dumblob/lingo_splix_board/design/evolution/v0.0.1_kbd-original_DE-s.jpg

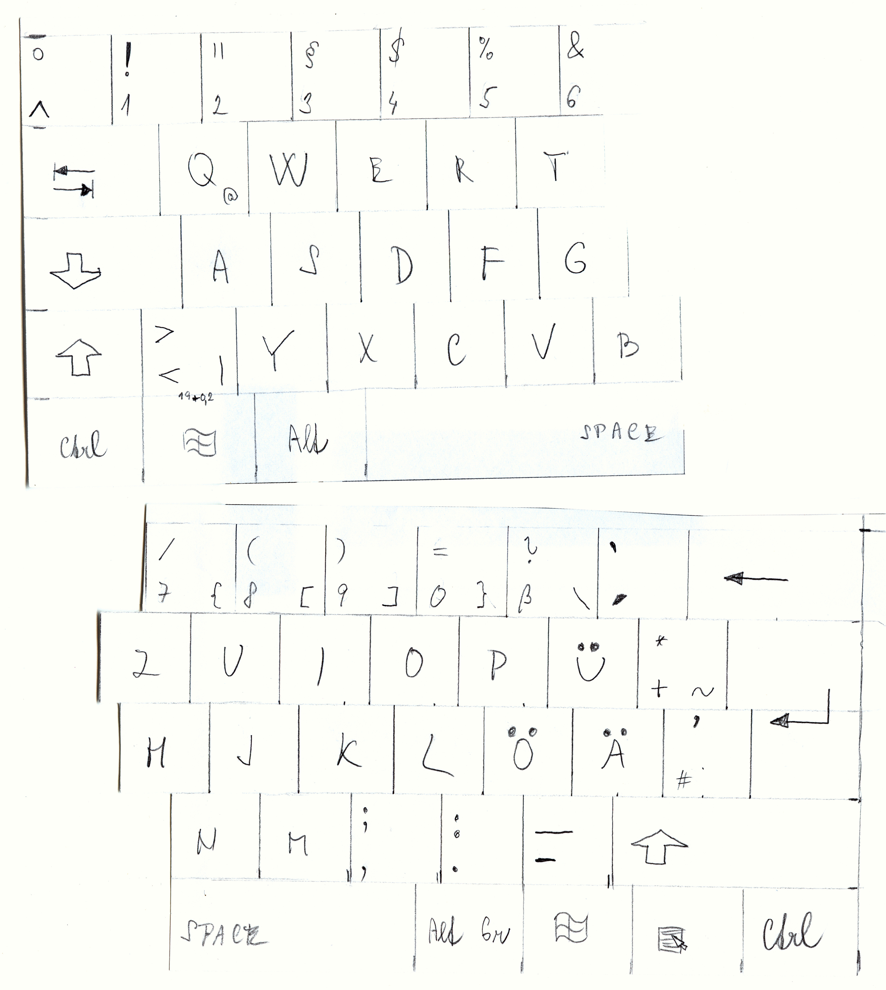
design/evolution/v0.0.1_kbd-original_DE-s.jpg
