dumblob/lingo_splix_board/design/evolution/v0.2_kbd-s.jpg

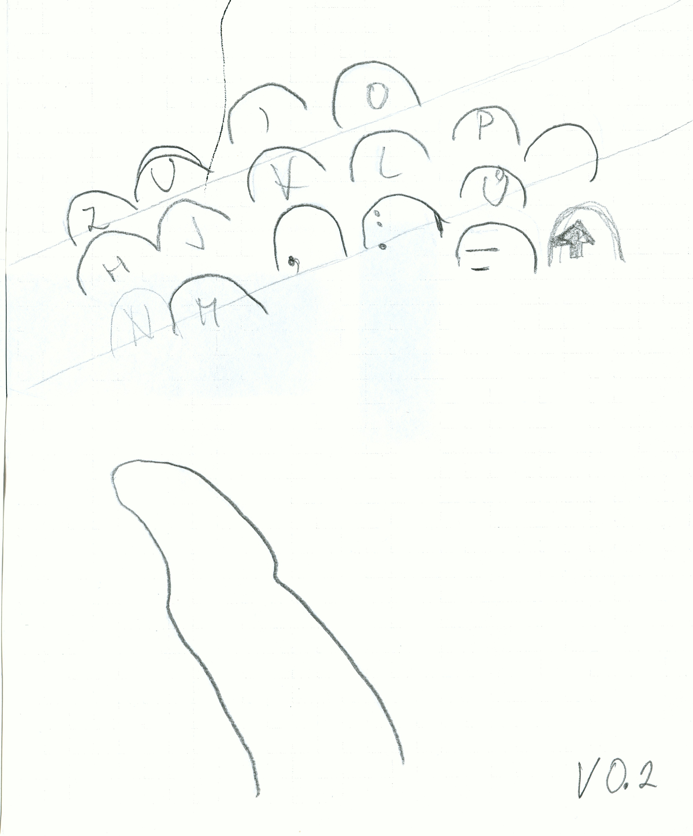
design/evolution/v0.2_kbd-s.jpg
