dumblob/lingo_splix_board/design/evolution/v0.3_kbd-s.jpg

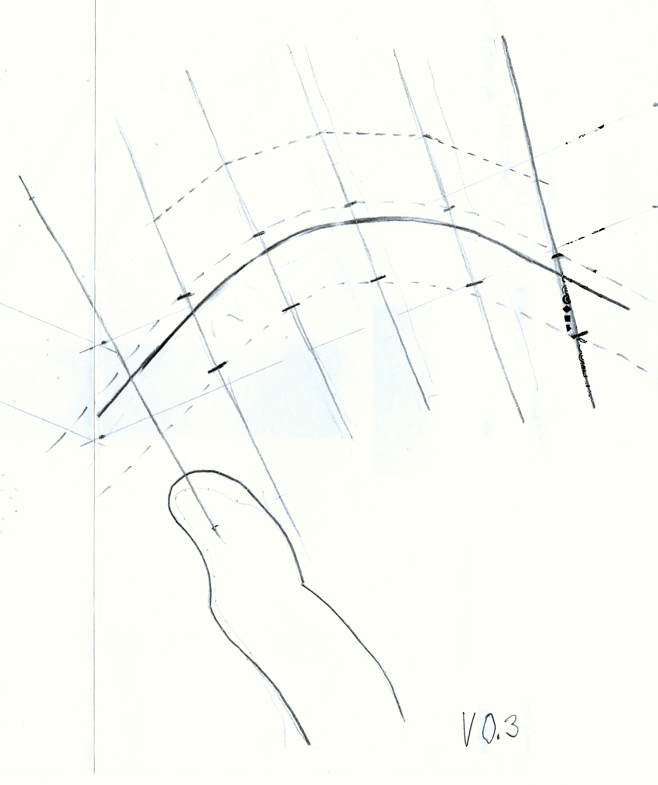
design/evolution/v0.3_kbd-s.jpg
