dumblob/lingo_splix_board/design/evolution/v0.4_kbd-s.jpg

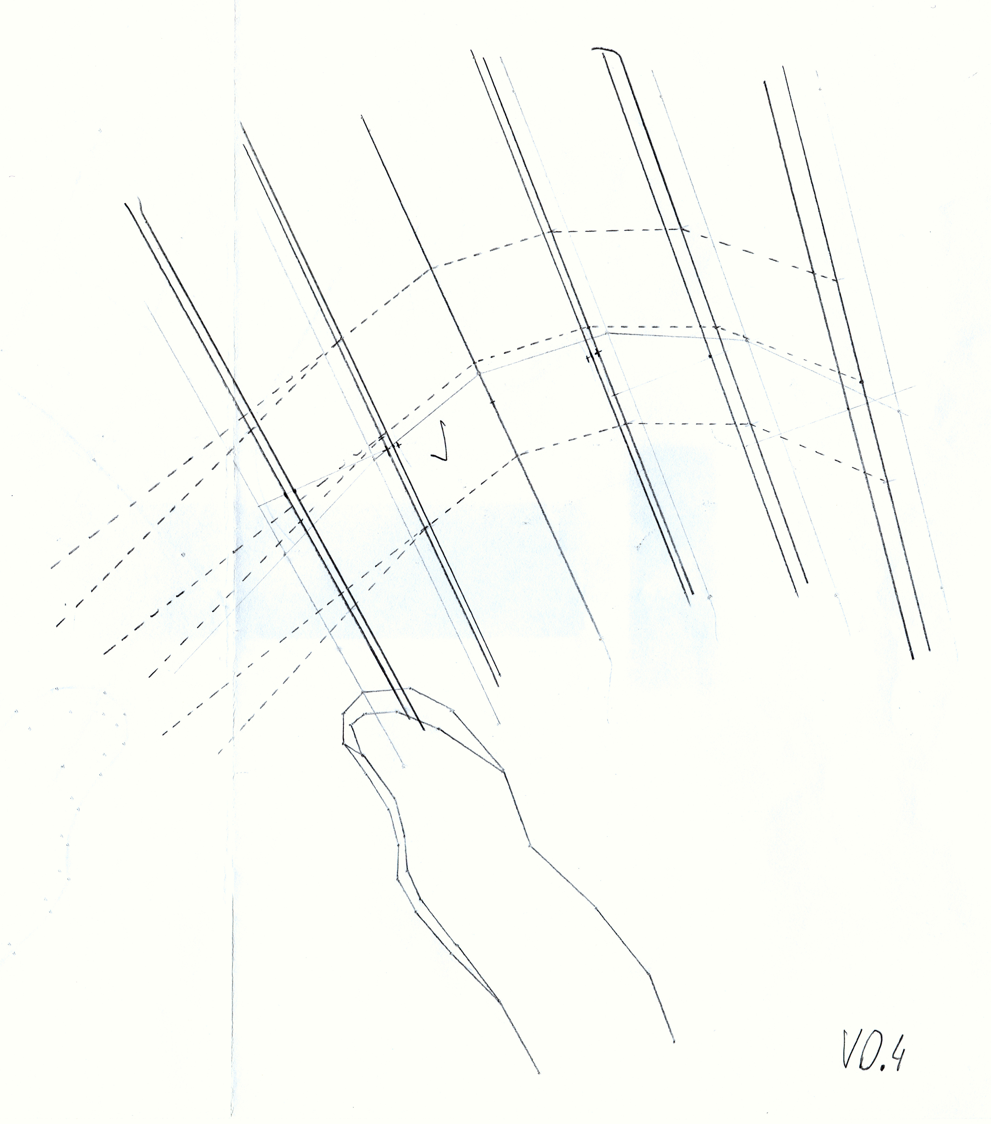
design/evolution/v0.4_kbd-s.jpg
