dumblob/lingo_splix_board/design/evolution/v0.6alpha1_kbd-s.jpg

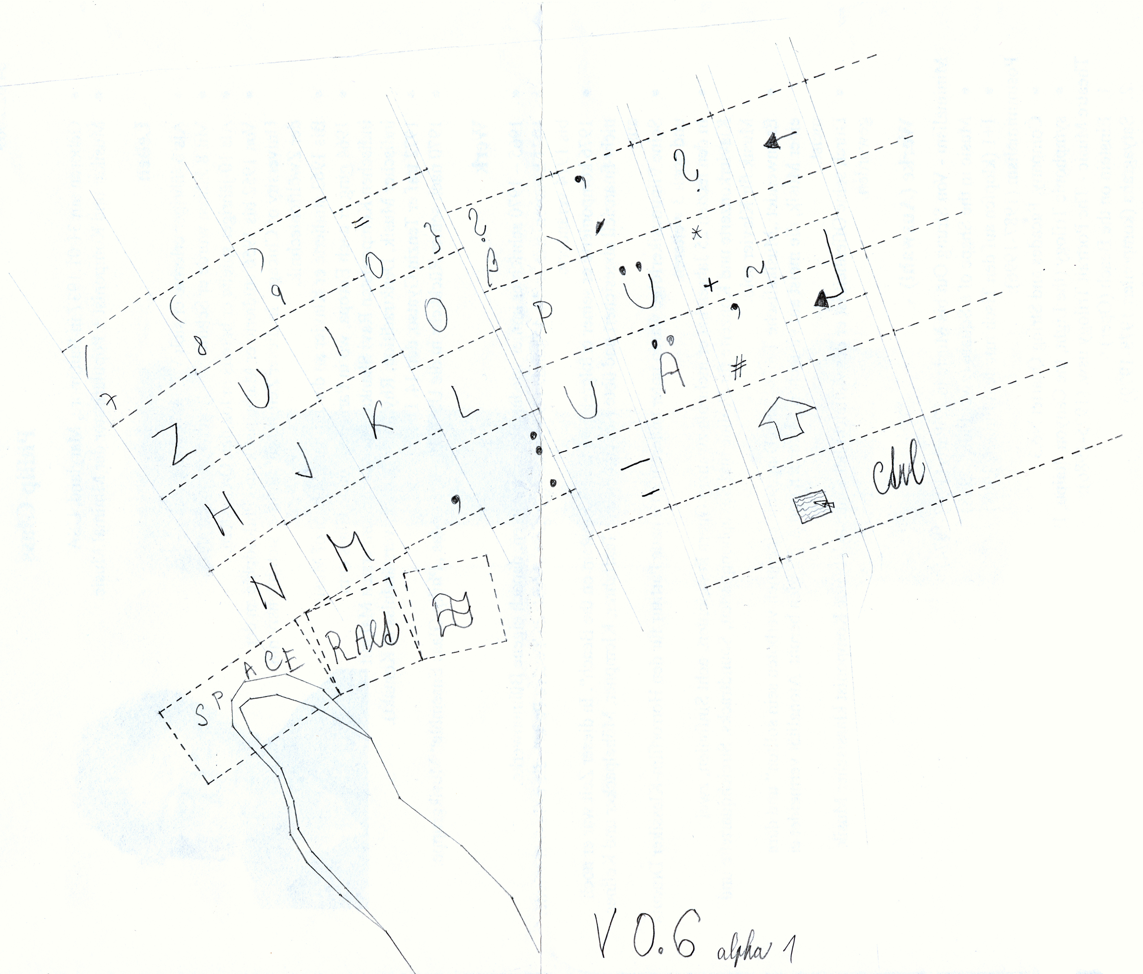
design/evolution/v0.6alpha1_kbd-s.jpg
