dumblob/lingo_splix_board/design/evolution/v0.7beta2_kbd_left-s.jpg

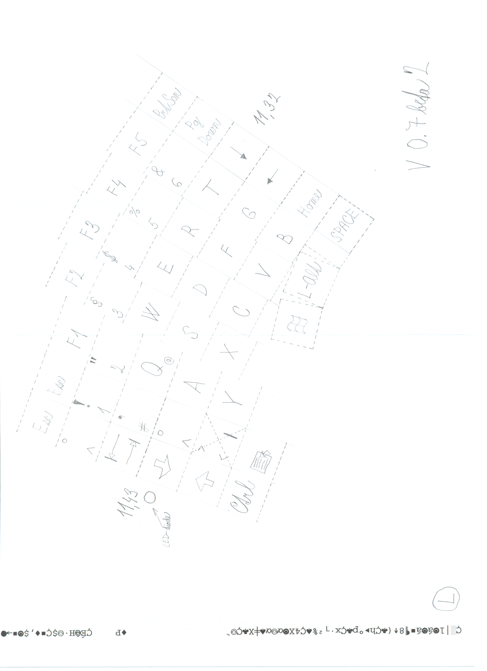
design/evolution/v0.7beta2_kbd_left-s.jpg
