dumblob/lingo_splix_board/design/evolution/v0.8_kbd_left-s.jpg

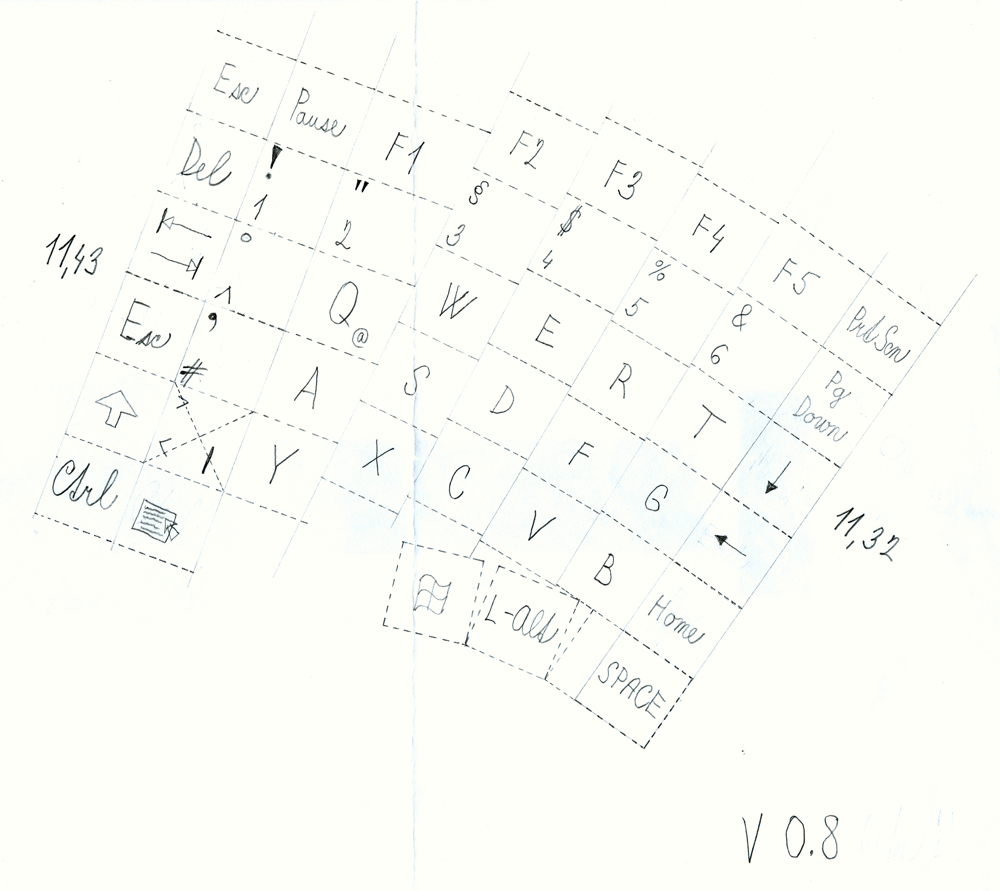
design/evolution/v0.8_kbd_left-s.jpg
