dumblob/lingo_splix_board/design/evolution/v0.9_kbd_left-s.jpg

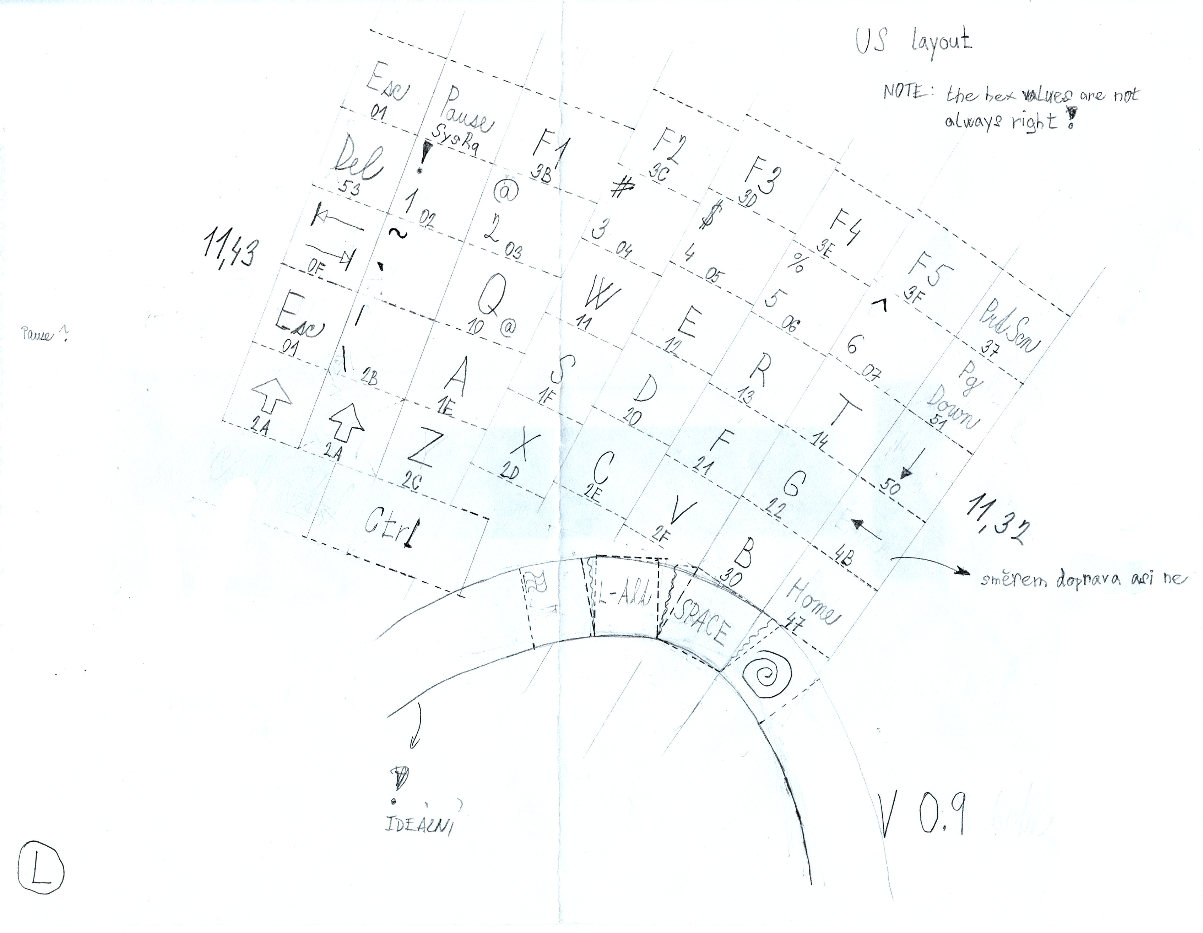
design/evolution/v0.9_kbd_left-s.jpg
