dumblob/lingo_splix_board/design/examples/800px-KB_Germany.svg.png

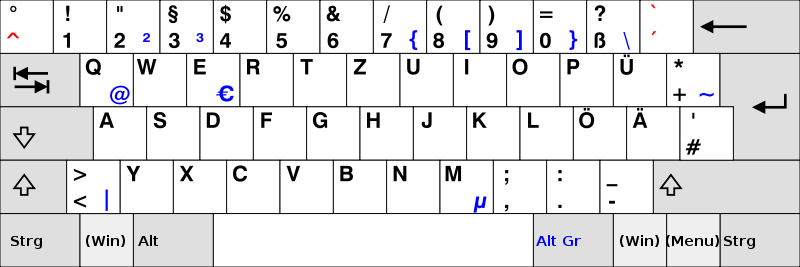
design/examples/800px-KB_Germany.svg.png
