dumblob/lingo_splix_board/design/examples/swirl_shifted_keys_proposal00.png

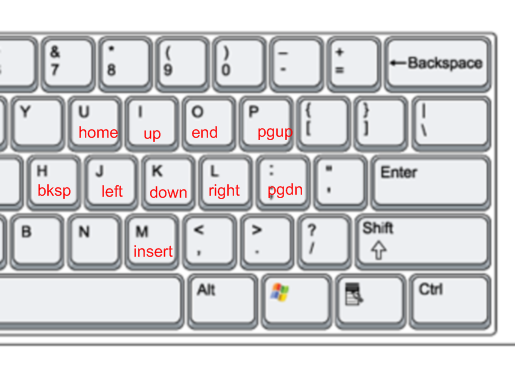
design/examples/swirl_shifted_keys_proposal00.png
