dumblob/lingo_splix_board/design/exports/v0.8_kbd_left_GE.png

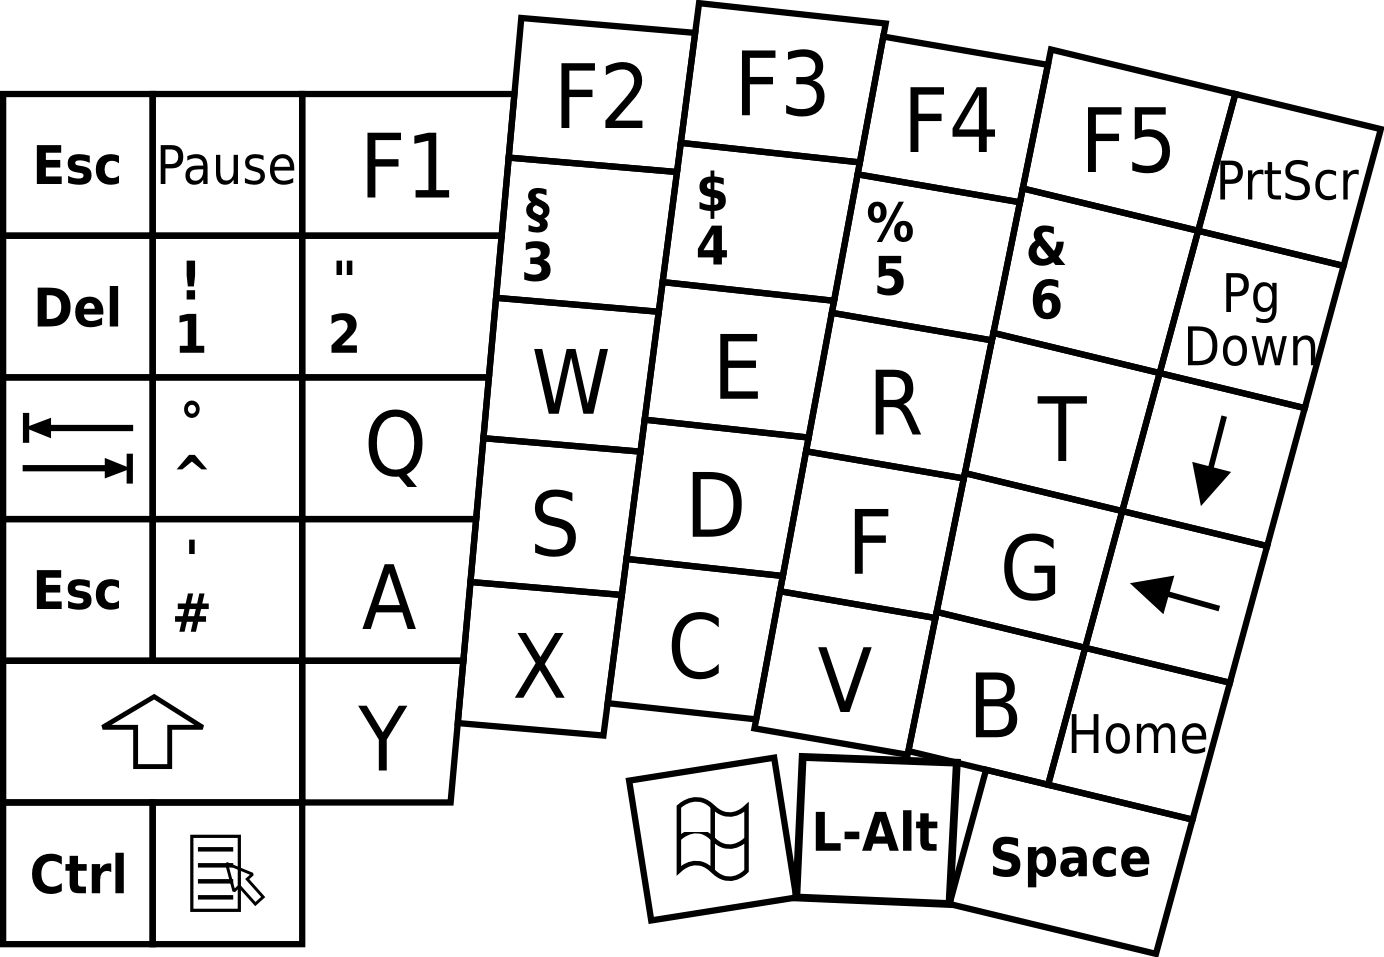
design/exports/v0.8_kbd_left_GE.png
