dumblob/lingo_splix_board/design/exports/v0.8_kbd_right_GE.png

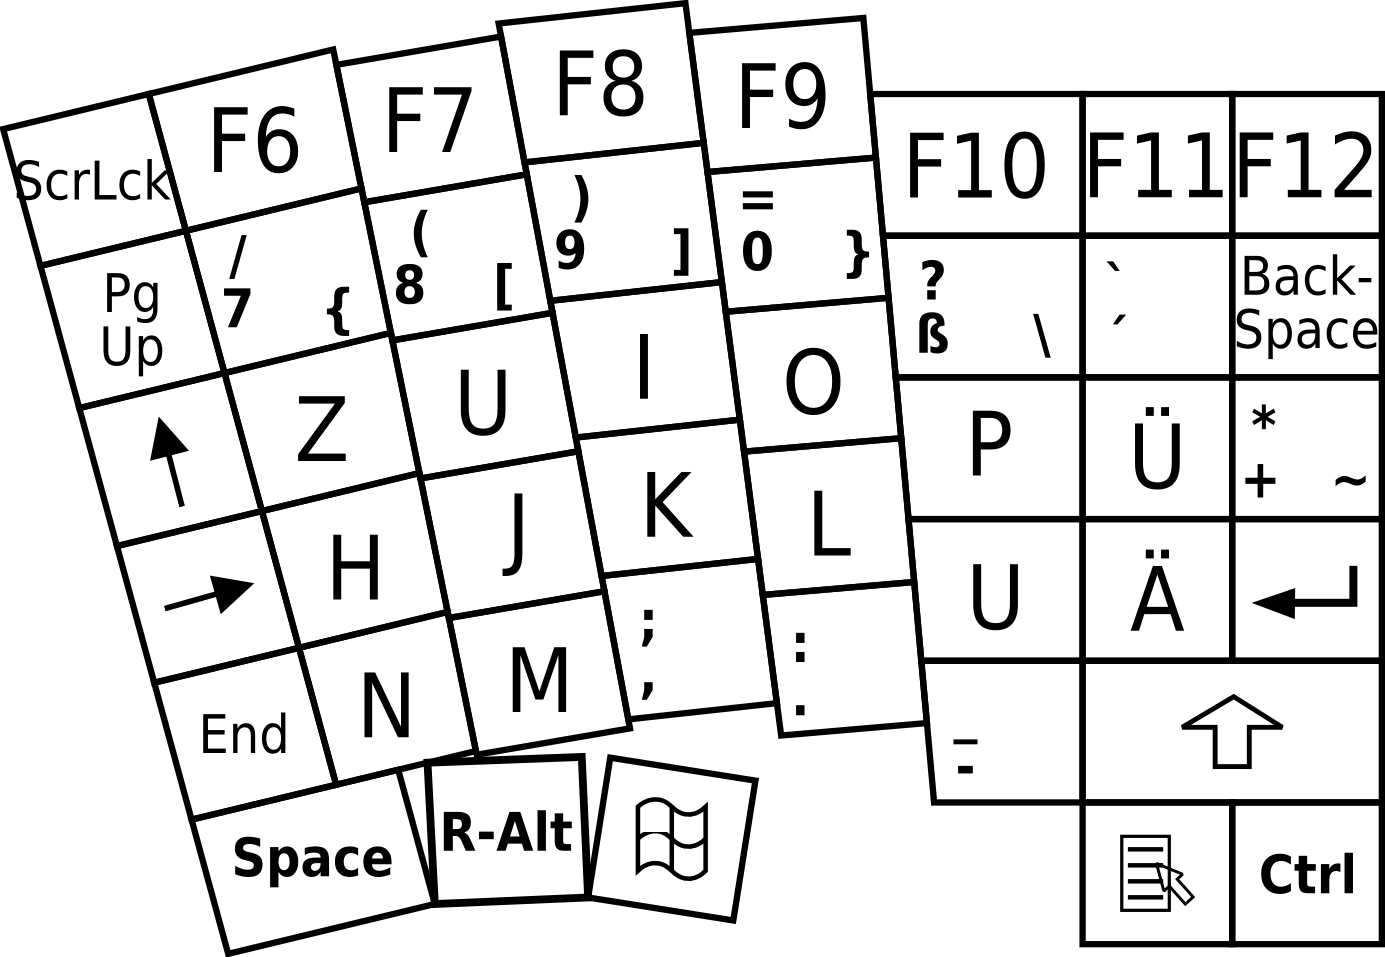
design/exports/v0.8_kbd_right_GE.png
