dumblob/lingo_splix_board/design/model/2016-01-20_19:59:37-overview.png

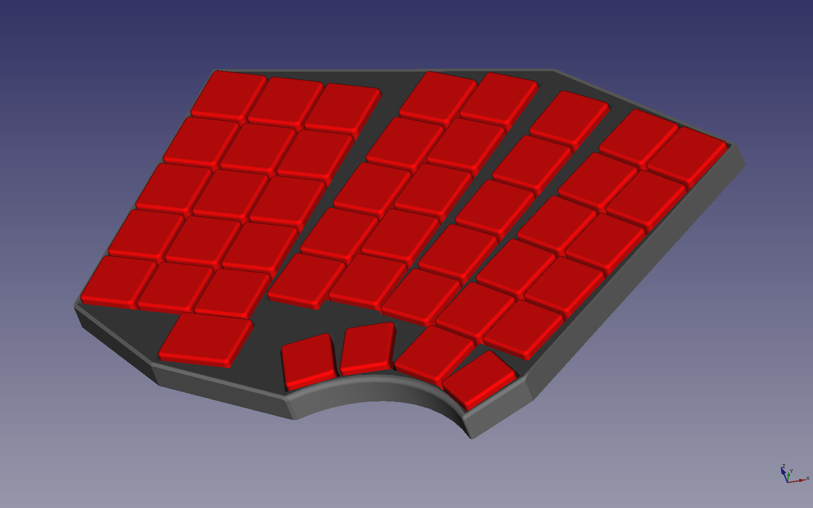
design/model/2016-01-20_19:59:37-overview.png
