dumblob/lingo_splix_board/design/model/2016-01-20_20:00:50-overview.png

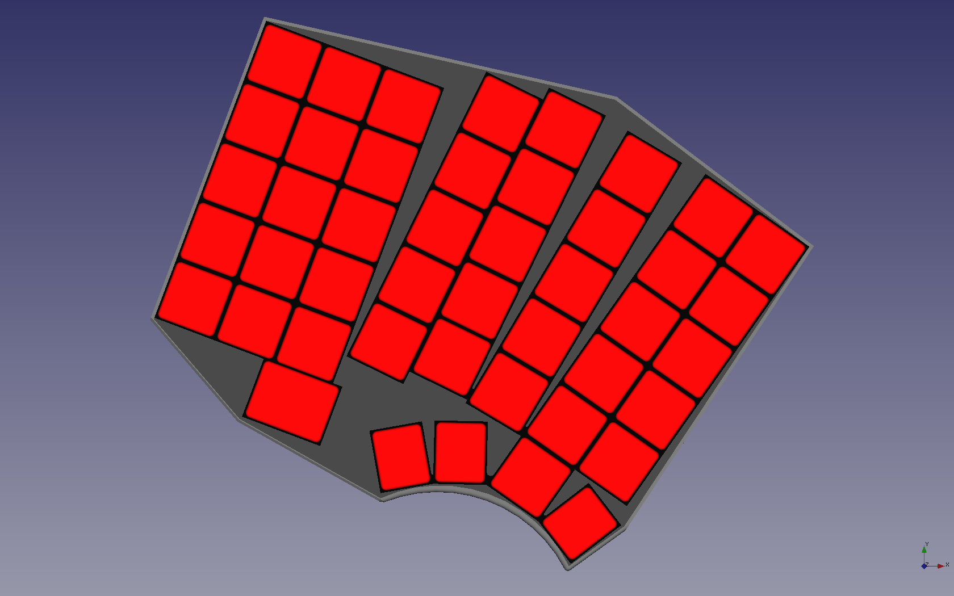
design/model/2016-01-20_20:00:50-overview.png
