dumblob/lingo_splix_board/design/model/201507181701-overview.png

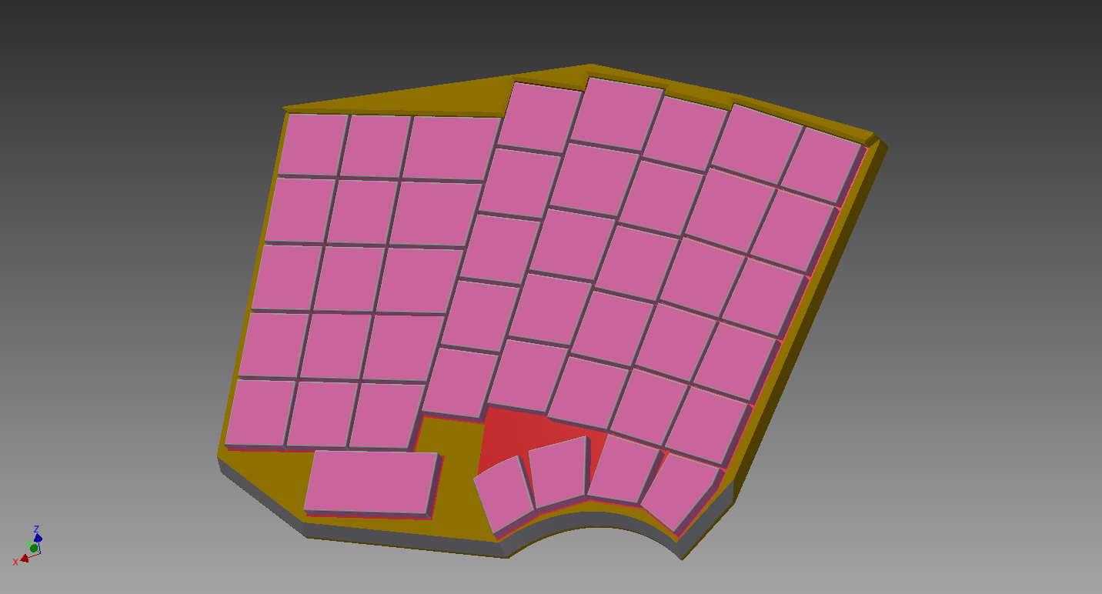
design/model/201507181701-overview.png
