dumblob/lingo_splix_board/design/model/201602232051-overview-no_caps.png

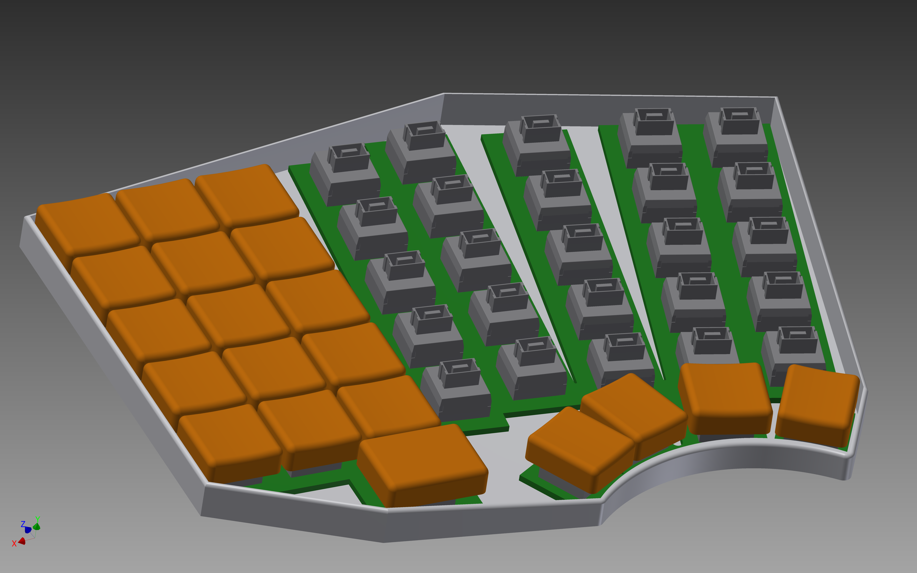
design/model/201602232051-overview-no_caps.png
