dumblob/lingo_splix_board/design/model/201602232053-overview.png

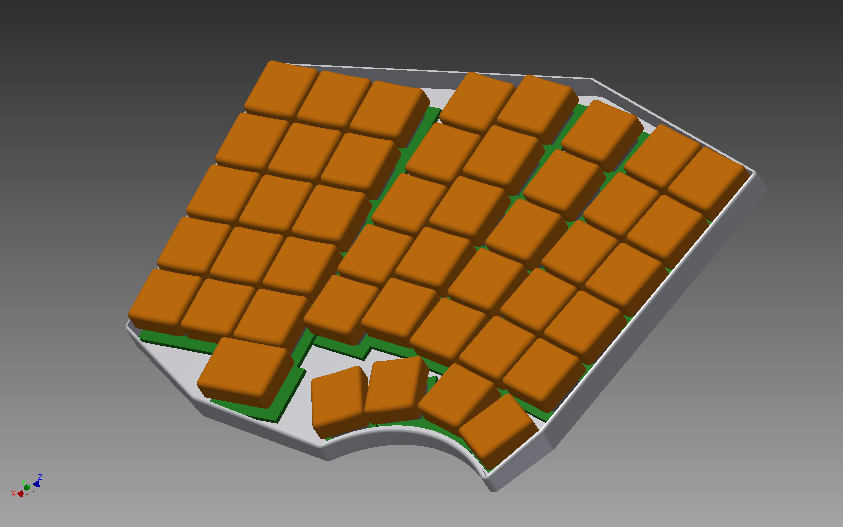
design/model/201602232053-overview.png
