dumblob/lingo_splix_board/design/model/201803212113-LSB_v0.1.1-left_part_with_mirrored_cut.png

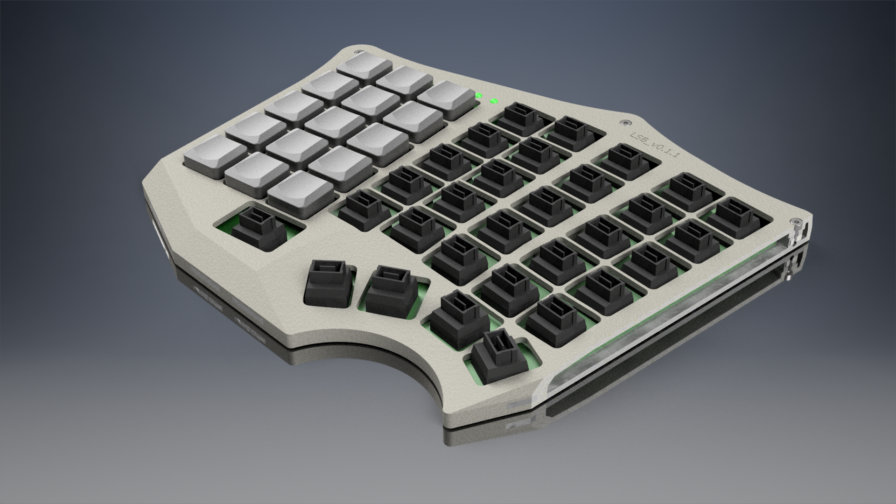
design/model/201803212113-LSB_v0.1.1-left_part_with_mirrored_cut.png
