dumblob/lingo_splix_board/hw/PR/20160522_125852.jpg

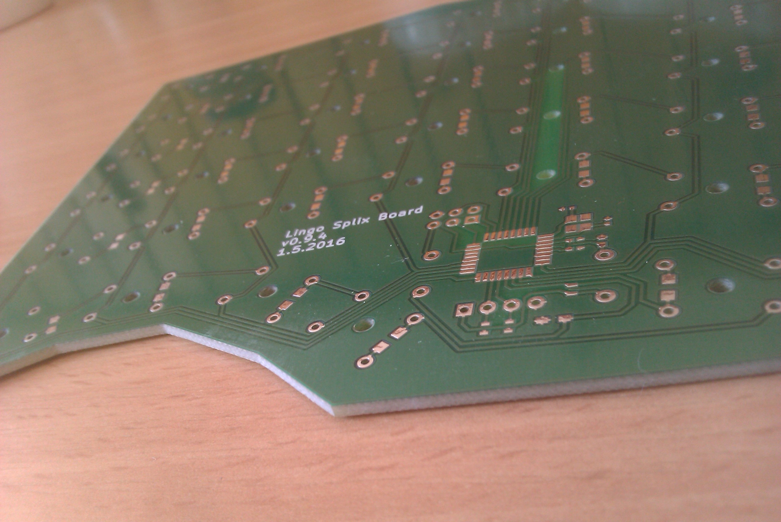
hw/PR/20160522_125852.jpg
