dumblob/lingo_splix_board/hw/PR/20160522_130012.jpg

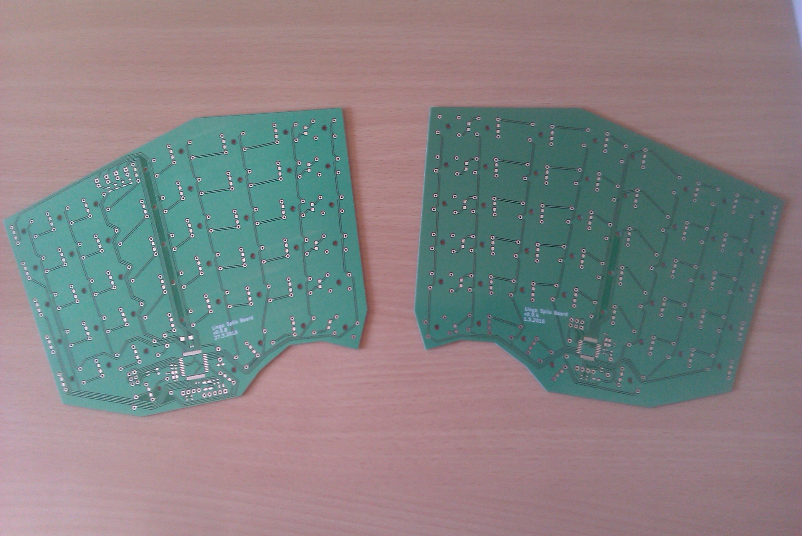
hw/PR/20160522_130012.jpg
