dumblob/lingo_splix_board/hw/PR/20160522_130031.jpg

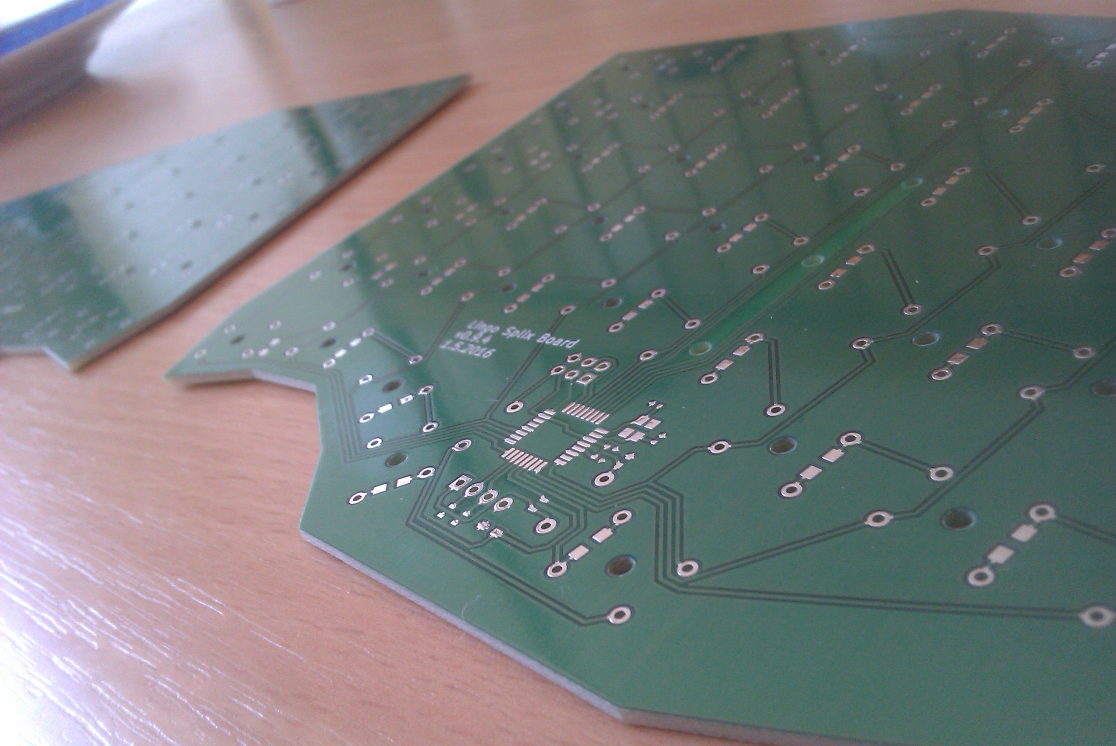
hw/PR/20160522_130031.jpg
