dumblob/lingo_splix_board/hw/PR/201602252030-sump.png

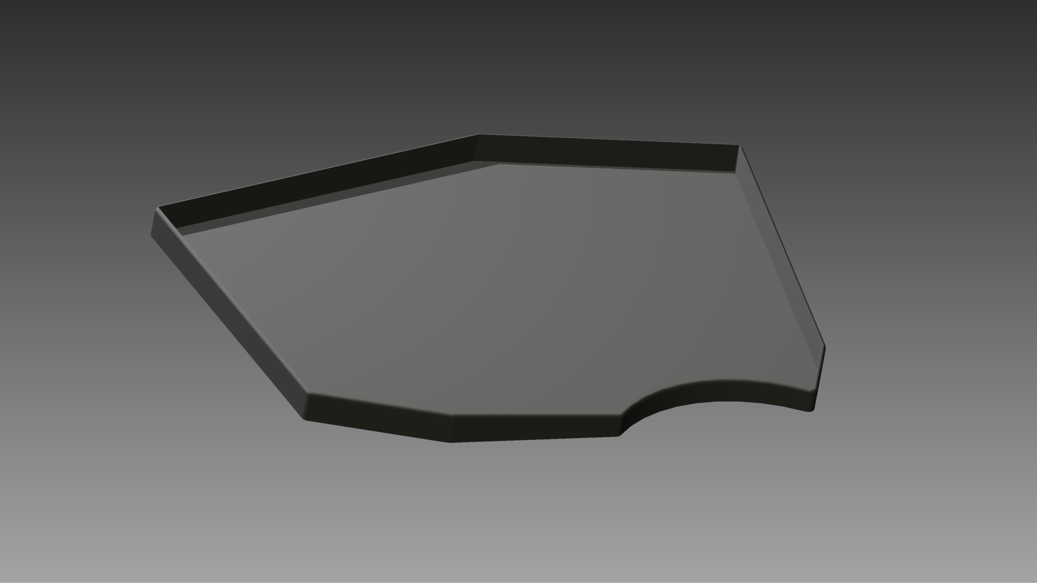
hw/PR/201602252030-sump.png
