dumblob/lingo_splix_board/hw/PR/201604212153-circuit.png

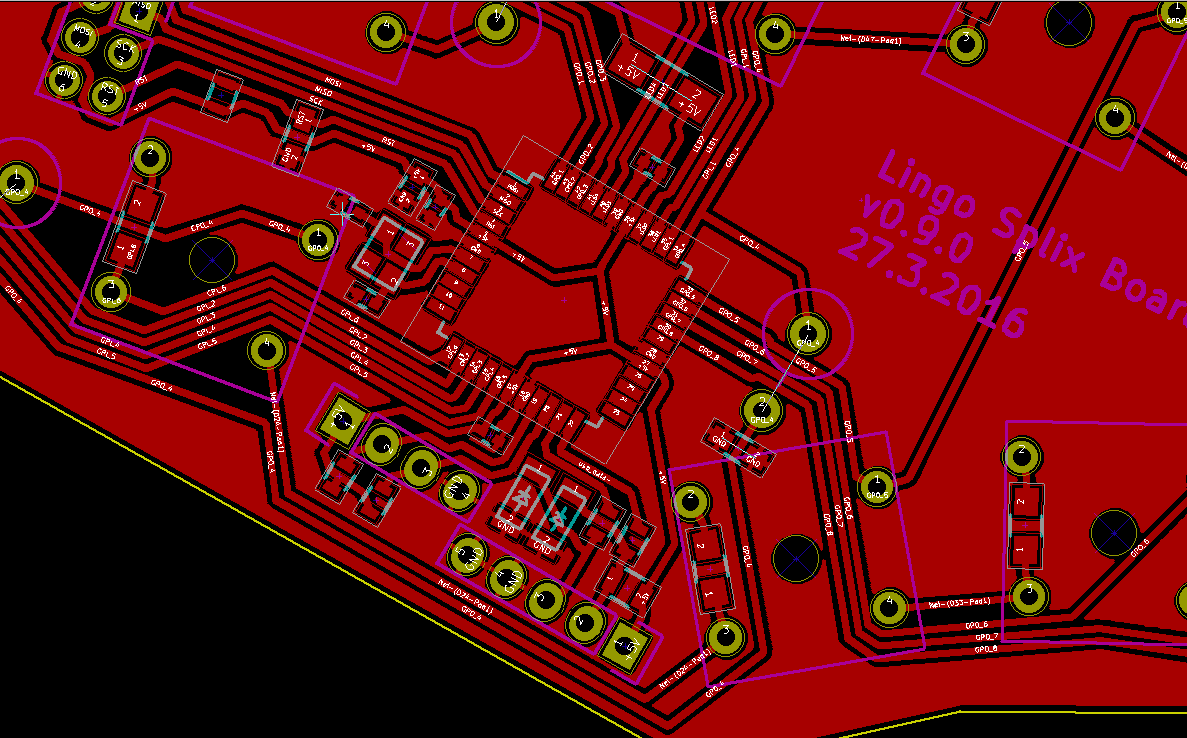
hw/PR/201604212153-circuit.png
