dumblob/lingo_splix_board/hw/PR/201604212154-circuit.png

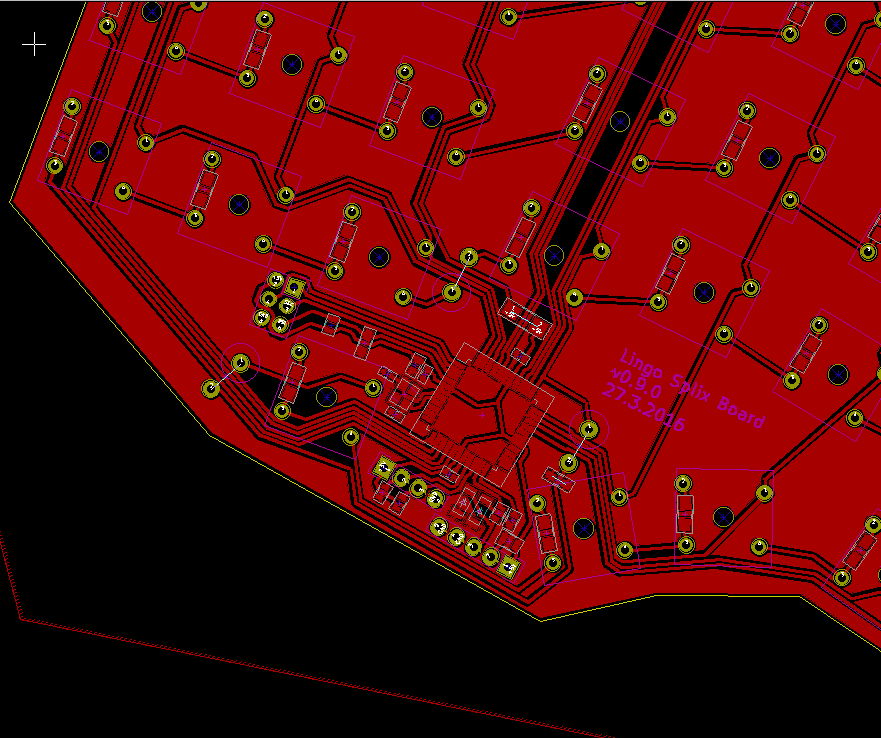
hw/PR/201604212154-circuit.png
