dumblob/lingo_splix_board/hw/PR/20150720170901-screenshot.png

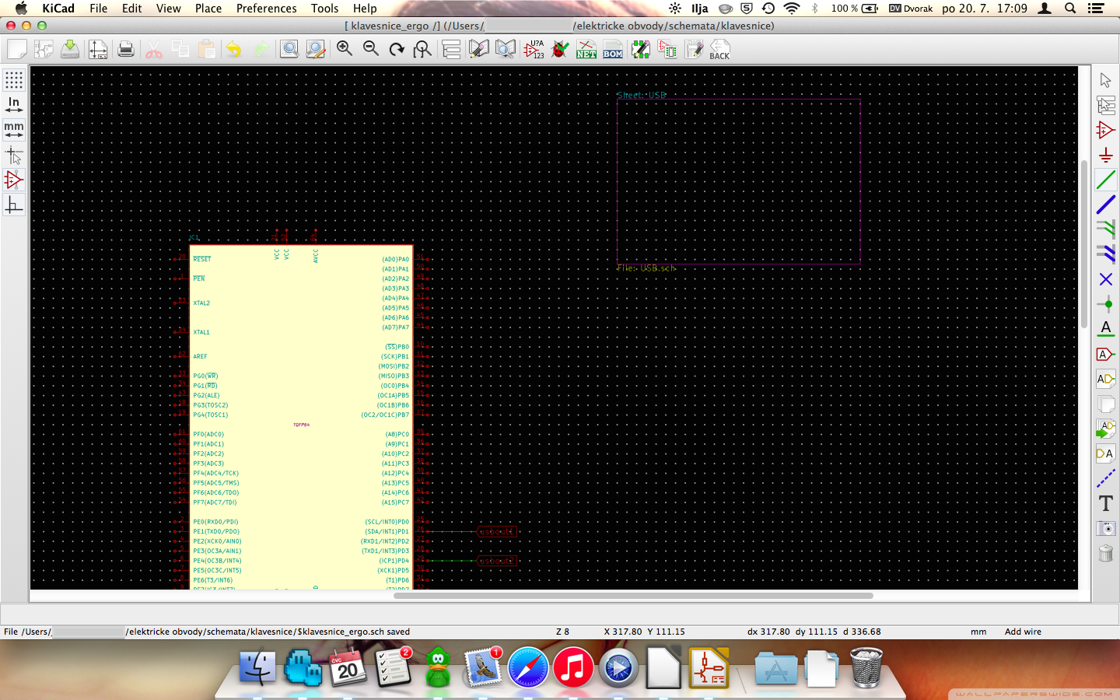
hw/PR/20150720170901-screenshot.png
