dumblob/lingo_splix_board/hw/PR/20150720170926-screenshot.png

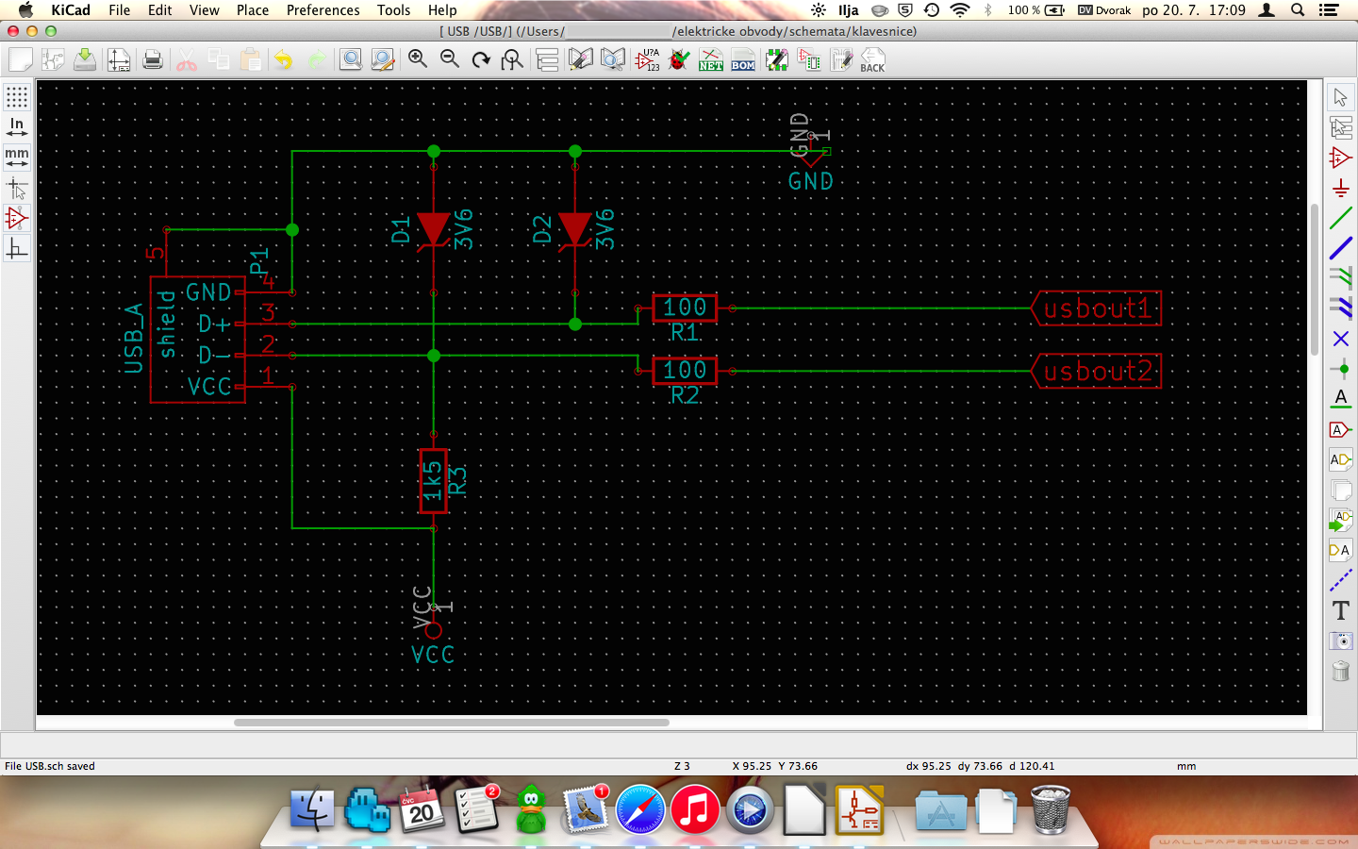
hw/PR/20150720170926-screenshot.png
