dumblob/lingo_splix_board/hw/PR/20150808175531-Pavel-CAD.jpg

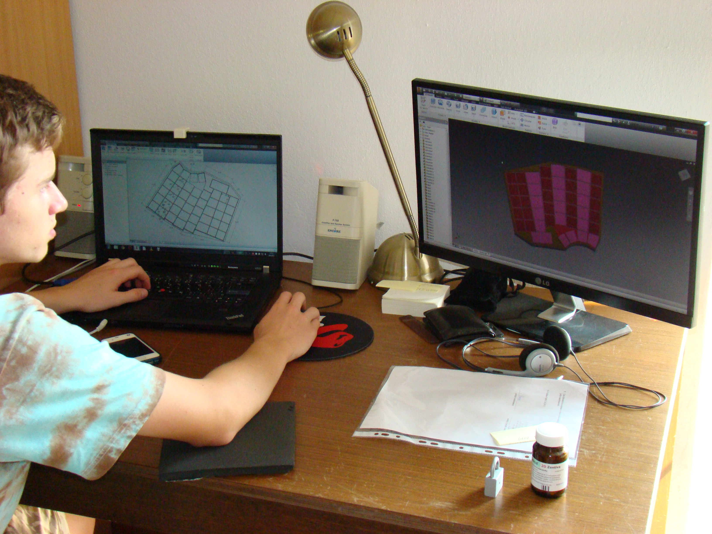
hw/PR/20150808175531-Pavel-CAD.jpg
