dumblob/lingo_splix_board/hw/PR/20160213212414-screenshot.png

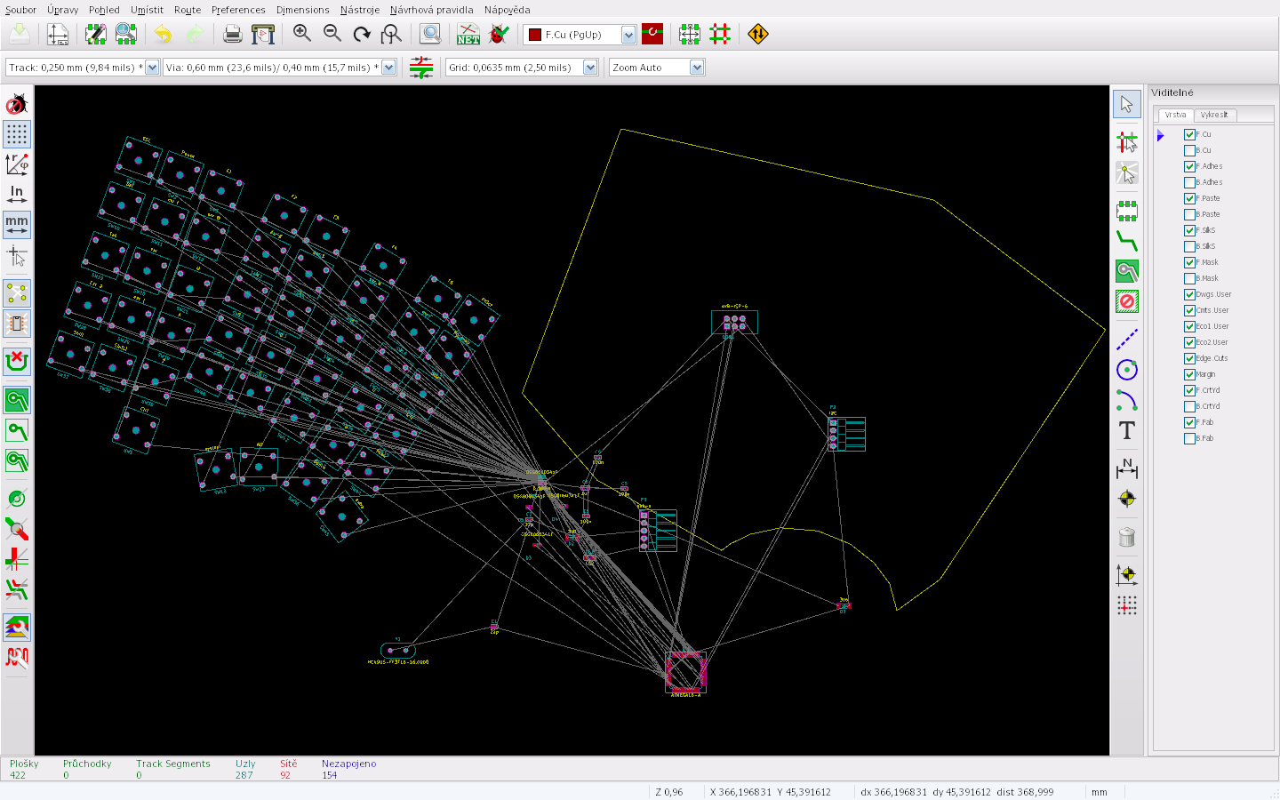
hw/PR/20160213212414-screenshot.png
