dumblob/lingo_splix_board/hw/PR/20160228174213-circuit.png

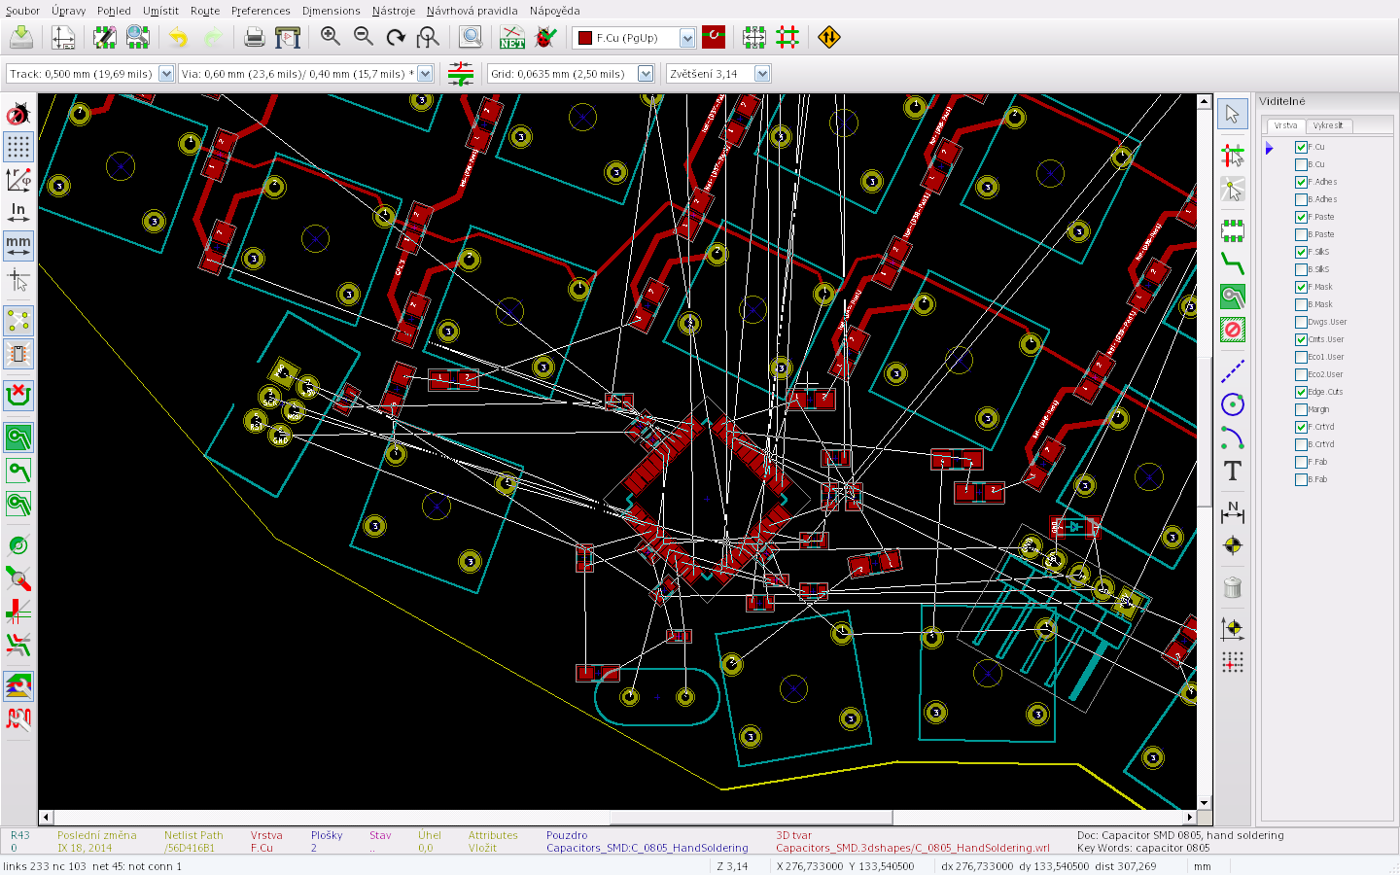
hw/PR/20160228174213-circuit.png
