dumblob/lingo_splix_board/doc/installation_of_diodes/diodes_kbd-00_m0110_115.jpg

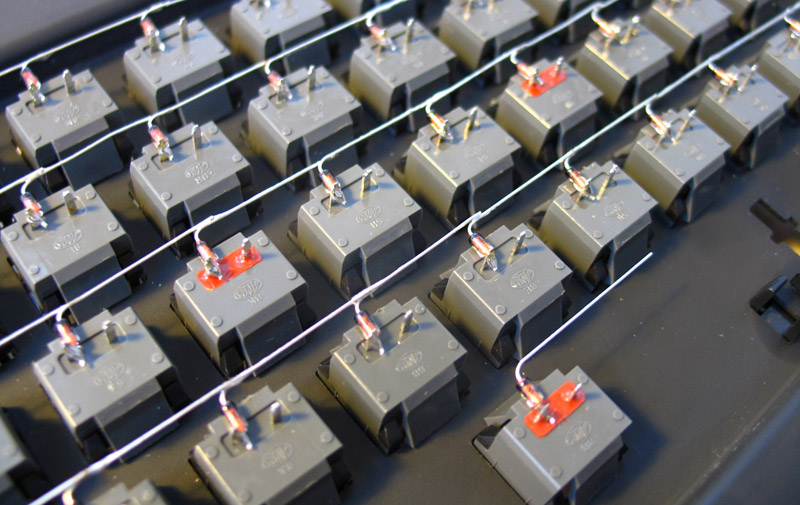
doc/installation_of_diodes/diodes_kbd-00_m0110_115.jpg
