dumblob/lingo_splix_board/doc/installation_of_diodes/diodes_kbd-01_m0110_120.jpg

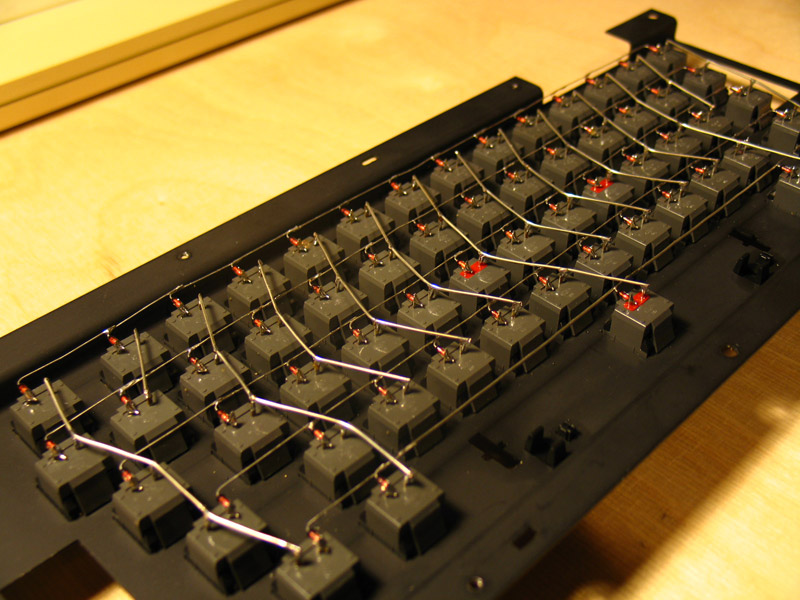
doc/installation_of_diodes/diodes_kbd-01_m0110_120.jpg
