dumblob/lingo_splix_board/doc/installation_of_diodes/diodes_kbd-02_m0110_130.jpg

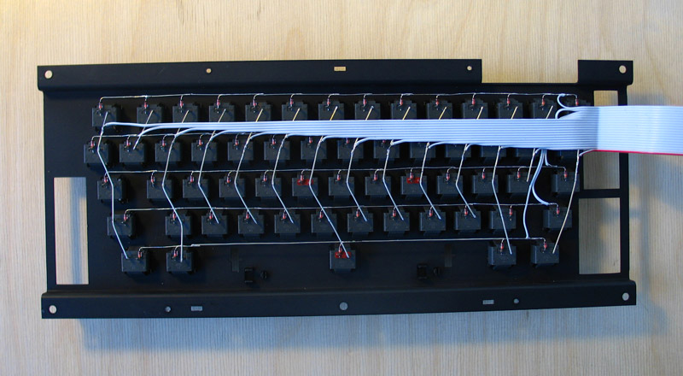
doc/installation_of_diodes/diodes_kbd-02_m0110_130.jpg
