dumblob/lingo_splix_board/hw/PR/201604081601-left_sump_3D_printed.jpg

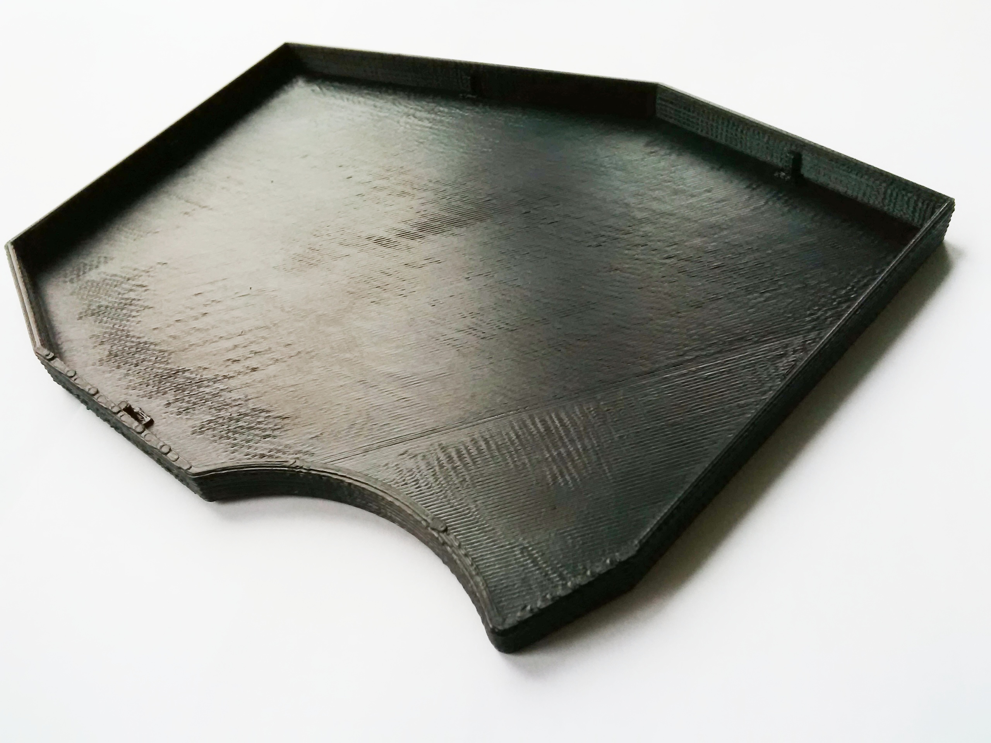
hw/PR/201604081601-left_sump_3D_printed.jpg
