dumblob/lingo_splix_board/hw/PCB/kbd_ergo_atmega16a.sch

## KiCad design hw/PCB/kbd_ergo_atmega16a.sch (2016-04-19)

Schematic: kbd_ergo_atmega16a.sch

Parts:
C1, C2: 22p; C_0402
C3, C4, C5: 100n; C_0402
C6: 1uF; C_0603
CON1: AVR-ISP-6; Pin_Header_Straight_2x03
D1, D2: 3V6; SOD-80C
D3, D4, D5, D6: LED; LED-3MM
D7, D8, D9, D10, D11, D12, D13, D14, D15, D16, D17, D18, D19, D20, D21, D22, D23, D24, D25, D26, D27, D28, D29, D30, D31, D32, D33, D34, D35, D36, D37, D38, D39, D40, D41, D42, D43, D44, D45, D46, D47, D48, D49, D50, D51: D_Small; R_0805_HandSoldering
GS1: GS2; R_0603_HandSoldering
IC1: ATMEGA16-A; TQFP-44_10x10mm_Pitch0.8mm
P1: usb-a; Pin_Header_Straight_1x05
P2: I2C; Pin_Header_Straight_1x04
R1: 1k5; R_0805
R2, R3: 100; R_0603
R4, R7, R9: 10k; R_0603
R5, R6, R8, R10: 1k; R_0805
R12: 0; R_0805
SW1, SW2, SW3, SW4, SW5, SW6, SW7, SW8: Cherry-button; ALPS-keyboard-f
SW9, SW10, SW11, SW12, SW13, SW14, SW15, SW16, SW17, SW18, SW19, SW20, SW21, SW22, SW23, SW24, SW25, SW26, SW27, SW28, SW29, SW30, SW31, SW32, SW33, SW34, SW35, SW36, SW37, SW38, SW39, SW40, SW41, SW42, SW43, SW44, SW45: Cherry-button; ALPS-keyboard
Y1: 16.00 MHz; crystal_FA238-TSX3225
